rvangelder11/Tube_Clock/code/Parola_Fonts_data.h

// Data file for UTF-8 example user defined fonts
#pragma once

MD_MAX72XX::fontType_t ExtASCII[] PROGMEM =
{
  0,		// 0 - 'Unused'
  0,		// 1 - 'Unused'
  0,		// 2 - 'Unused'
  0,		// 3 - 'Unused'
  0,		// 4 - 'Unused'
  0,		// 5 - 'Unused'
  0,		// 6 - 'Unused'
  0,		// 7 - 'Unused'
  0,		// 8 - 'Unused'
  0,		// 9 - 'Unused'
  0,		// 10 - 'Unused'
  0,		// 11 - 'Unused'
  0,		// 12 - 'Unused'
  0,		// 13 - 'Unused'
  0,		// 14 - 'Unused'
  0,		// 15 - 'Unused'
  0,		// 16 - 'Unused'
  0,		// 17 - 'Unused'
  0,		// 18 - 'Unused'
  0,		// 19 - 'Unused'
  0,		// 20 - 'Unused'
  0,		// 21 - 'Unused'
  0,		// 22 - 'Unused'
  0,		// 23 - 'Unused'
  0,		// 24 - 'Unused'
  0,		// 25 - 'Unused'
  0,		// 26 - 'Unused'
  0,		// 27 - 'Unused'
  0,		// 28 - 'Unused'
  0,		// 29 - 'Unused'
  0,		// 30 - 'Unused'
  0,		// 31 - 'Unused'
  2, 0, 0,		// 32 - 'Space'
  1, 95,		// 33 - '!'
  3, 7, 0, 7,		// 34 - '"'
  5, 20, 127, 20, 127, 20,		// 35 - '#'
  5, 36, 42, 127, 42, 18,		// 36 - '$'
  5, 35, 19, 8, 100, 98,		// 37 - '%'
  5, 54, 73, 86, 32, 80,		// 38 - '&'
  2, 4, 3,		// 39
  3, 28, 34, 65,		// 40 - '('
  3, 65, 34, 28,		// 41 - ')'
  5, 42, 28, 127, 28, 42,		// 42 - '*'
  5, 8, 8, 62, 8, 8,		// 43 - '+'
  2, 128, 96,		// 44 - ','
  5, 8, 8, 8, 8, 8,		// 45 - '-'
  2, 96, 96,		// 46 - '.'
  5, 32, 16, 8, 4, 2,		// 47 - '/'
  5, 62, 81, 73, 69, 62,		// 48 - '0'
  3, 66, 127, 64,		// 49 - '1'
  5, 114, 73, 73, 73, 70,		// 50 - '2'
  5, 33, 65, 73, 77, 51,		// 51 - '3'
  5, 24, 20, 18, 127, 16,		// 52 - '4'
  5, 39, 69, 69, 69, 57,		// 53 - '5'
  5, 60, 74, 73, 73, 49,		// 54 - '6'
  5, 65, 33, 17, 9, 7,		// 55 - '7'
  5, 54, 73, 73, 73, 54,		// 56 - '8'
  5, 70, 73, 73, 41, 30,		// 57 - '9'
  1, 20,		// 58 - ':'
  2, 128, 104,		// 59 - ';'
  4, 8, 20, 34, 65,		// 60 - '<'
  5, 20, 20, 20, 20, 20,		// 61 - '='
  4, 65, 34, 20, 8,		// 62 - '>'
  5, 2, 1, 89, 9, 6,		// 63 - '?'
  5, 62, 65, 93, 89, 78,		// 64 - '@'
  5, 124, 18, 17, 18, 124,		// 65 - 'A'
  5, 127, 73, 73, 73, 54,		// 66 - 'B'
  5, 62, 65, 65, 65, 34,		// 67 - 'C'
  5, 127, 65, 65, 65, 62,		// 68 - 'D'
  5, 127, 73, 73, 73, 65,		// 69 - 'E'
  5, 127, 9, 9, 9, 1,		// 70 - 'F'
  5, 62, 65, 65, 81, 115,		// 71 - 'G'
  5, 127, 8, 8, 8, 127,		// 72 - 'H'
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
  0,		// 127 - 'Unused'
  6, 20, 62, 85, 85, 65, 34,		// 128 - 'Euro sign'
  0,		// 129 - 'Not used'
  2, 128, 96,		// 130 - 'Single low 9 quotation mark'
  5, 192, 136, 126, 9, 3,		// 131 - 'f with hook'
  4, 128, 96, 128, 96,		// 132 - 'Single low 9 quotation mark'
  8, 96, 96, 0, 96, 96, 0, 96, 96,		// 133 - 'Horizontal ellipsis'
  3, 4, 126, 4,		// 134 - 'Dagger'
  3, 20, 126, 20,		// 135 - 'Double dagger'
  4, 2, 1, 1, 2,		// 136 - 'Modifier circumflex'
  7, 35, 19, 104, 100, 2, 97, 96,		// 137 - 'Per mille sign'
  5, 72, 85, 86, 85, 36,		// 138 - 'S with caron'
  3, 8, 20, 34,		// 139 - '< quotation'
  6, 62, 65, 65, 127, 73, 73,		// 140 - 'OE'
  0,		// 141 - 'Not used'
  5, 68, 101, 86, 77, 68,		// 142 - 'z with caron'
  0,		// 143 - 'Not used'
  0,		// 144 - 'Not used'
  2, 3, 4,		// 145 - 'Left single quote mark'
  2, 4, 3,		// 146 - 'Right single quote mark'
  4, 3, 4, 3, 4,		// 147 - 'Left double quote marks'
  4, 4, 3, 4, 3,		// 148 - 'Right double quote marks'
  4, 0, 24, 60, 24,		// 149 - 'Bullet Point'
  3, 8, 8, 8,		// 150 - 'En dash'
  5, 8, 8, 8, 8, 8,		// 151 - 'Em dash'
  4, 2, 1, 2, 1,		// 152 - 'Small ~'
  7, 1, 15, 1, 0, 15, 2, 15,		// 153 - 'TM'
  5, 72, 85, 86, 85, 36,		// 154 - 's with caron'
  3, 34, 20, 8,		// 155 - '> quotation'
  7, 56, 68, 68, 124, 84, 84, 8,		// 156 - 'oe'
  0,		// 157 - 'Not used'
  5, 68, 101, 86, 77, 68,		// 158 - 'z with caron'
  5, 12, 17, 96, 17, 12,		// 159 - 'Y diaresis'
  2, 0, 0,		// 160 - 'Non-breaking space'
  1, 125,		// 161 - 'Inverted !'
  5, 60, 36, 126, 36, 36,		// 162 - 'Cent sign'
  5, 72, 126, 73, 65, 102,		// 163 - 'Pound sign'
  5, 34, 28, 20, 28, 34,		// 164 - 'Currency sign'
  5, 43, 47, 252, 47, 43,		// 165 - 'Yen'
  1, 119,		// 166 - '|'
  4, 102, 137, 149, 106,		// 167 - 'Section sign'
  3, 1, 0, 1,		// 168 - 'Spacing diaresis'
  7, 62, 65, 93, 85, 85, 65, 62,		// 169 - 'Copyright'
  3, 13, 13, 15,		// 170 - 'Feminine Ordinal Ind.'
  5, 8, 20, 42, 20, 34,		// 171 - '<<'
  5, 8, 8, 8, 8, 56,		// 172 - 'Not sign'
  0,		// 173 - 'Soft Hyphen'
  7, 62, 65, 127, 75, 117, 65, 62,		// 174 - 'Registered Trademark'
  5, 1, 1, 1, 1, 1,		// 175 - 'Spacing Macron Overline'
  3, 2, 5, 2,		// 176 - 'Degree'
  5, 68, 68, 95, 68, 68,		// 177 - '+/-'
  3, 25, 21, 19,		// 178 - 'Superscript 2'
  3, 17, 21, 31,		// 179 - 'Superscript 3'
  2, 2, 1,		// 180 - 'Acute accent'
  4, 252, 64, 64, 60,		// 181 - 'micro (mu)'
  5, 6, 9, 127, 1, 127,		// 182 - 'Paragraph Mark'
  2, 24, 24,		// 183 - 'Middle Dot'
  3, 128, 128, 96,		// 184 - 'Spacing sedilla'
  2, 2, 31,		// 185 - 'Superscript 1'
  4, 6, 9, 9, 6,		// 186 - 'Masculine Ordinal Ind.'
  5, 34, 20, 42, 20, 8,		// 187 - '>>'
  6, 64, 47, 16, 40, 52, 250,		// 188 - '1/4'
  6, 64, 47, 16, 200, 172, 186,		// 189 - '1/2'
  6, 85, 53, 31, 40, 52, 250,		// 190 - '3/4'
  5, 48, 72, 77, 64, 32,		// 191 - 'Inverted ?'
  5, 120, 20, 21, 22, 120,		// 192 - 'A grave'
  5, 120, 22, 21, 20, 120,		// 193 - 'A acute'
  5, 122, 21, 21, 21, 122,		// 194 - 'A circumflex'
  5, 120, 22, 21, 22, 121,		// 195 - 'A tilde'
  5, 120, 21, 20, 21, 120,		// 196 - 'A diaresis'
  5, 120, 20, 21, 20, 120,		// 197 - 'A ring above'
  6, 124, 10, 9, 127, 73, 73,		// 198 - 'AE'
  5, 30, 161, 161, 97, 18,		// 199 - 'C sedilla'
  4, 124, 85, 86, 68,		// 200 - 'E grave'
  4, 124, 86, 85, 68,		// 201 - 'E acute'
  4, 126, 85, 85, 70,		// 202 - 'E circumflex'
  4, 124, 85, 84, 69,		// 203 - 'E diaresis'
  3, 68, 125, 70,		// 204 - 'I grave'
  3, 68, 126, 69,		// 205 - 'I acute'
  3, 70, 125, 70,		// 206 - 'I circumplex'
  3, 69, 124, 69,		// 207 - 'I diaresis'
  6, 4, 127, 69, 65, 65, 62,		// 208 - 'Capital Eth'
  5, 124, 10, 17, 34, 125,		// 209 - 'N tilde'
  5, 56, 68, 69, 70, 56,		// 210 - 'O grave'
  5, 56, 70, 69, 68, 56,		// 211 - 'O acute'
  5, 58, 69, 69, 69, 58,		// 212 - 'O circumflex'
  5, 56, 70, 69, 70, 57,		// 213 - 'O tilde'
  5, 56, 69, 68, 69, 56,		// 214 - 'O diaresis'
  5, 34, 20, 8, 20, 34,		// 215 - 'Multiplication sign'
  7, 64, 62, 81, 73, 69, 62, 1,		// 216 - 'O slashed'
  5, 60, 65, 66, 64, 60,		// 217 - 'U grave'
  5, 60, 64, 66, 65, 60,		// 218 - 'U acute'
  5, 58, 65, 65, 65, 58,		// 219 - 'U circumflex'
  5, 60, 65, 64, 65, 60,		// 220 - 'U diaresis'
  5, 12, 16, 98, 17, 12,		// 221 - 'Y acute'
  4, 127, 18, 18, 12,		// 222 - 'Capital thorn'
  4, 254, 37, 37, 26,		// 223 - 'Small letter sharp S'
  5, 32, 84, 85, 122, 64,		// 224 - 'a grave'
  5, 32, 84, 86, 121, 64,		// 225 - 'a acute'
  5, 34, 85, 85, 121, 66,		// 226 - 'a circumflex'
  5, 32, 86, 85, 122, 65,		// 227 - 'a tilde'
  5, 32, 85, 84, 121, 64,		// 228 - 'a diaresis'
  5, 32, 84, 85, 120, 64,		// 229 - 'a ring above'
  7, 32, 84, 84, 124, 84, 84, 8,		// 230 - 'ae'
  5, 24, 36, 164, 228, 40,		// 231 - 'c sedilla'
  5, 56, 84, 85, 86, 88,		// 232 - 'e grave'
  5, 56, 84, 86, 85, 88,		// 233 - 'e acute'
  5, 58, 85, 85, 85, 90,		// 234 - 'e circumflex'
  5, 56, 85, 84, 85, 88,		// 235 - 'e diaresis'
  3, 68, 125, 66,		// 236 - 'i grave'
  3, 68, 126, 65,		// 237 - 'i acute'
  3, 70, 125, 66,		// 238 - 'i circumflex'
  3, 69, 124, 65,		// 239 - 'i diaresis'
  4, 48, 75, 74, 61,		// 240 - 'Small eth'
  4, 122, 9, 10, 113,		// 241 - 'n tilde'
  5, 56, 68, 69, 70, 56,		// 242 - 'o grave'
  5, 56, 70, 69, 68, 56,		// 243 - 'o acute'
  5, 58, 69, 69, 69, 58,		// 244 - 'o circumflex'
  5, 56, 70, 69, 70, 57,		// 245 - 'o tilde'
  5, 56, 69, 68, 69, 56,		// 246 - 'o diaresis'
  5, 8, 8, 42, 8, 8,		// 247 - 'Division sign'
  6, 64, 56, 84, 76, 68, 58,		// 248 - 'o slashed'
  5, 60, 65, 66, 32, 124,		// 249 - 'u grave'
  5, 60, 64, 66, 33, 124,		// 250 - 'u acute'
  5, 58, 65, 65, 33, 122,		// 251 - 'u circumflex'
  5, 60, 65, 64, 33, 124,		// 252 - 'u diaresis'
  4, 156, 162, 161, 124,		// 253 - 'y acute'
  4, 252, 72, 72, 48,		// 254 - 'small thorn'
  4, 157, 160, 160, 125,		// 255 - 'y diaresis'
};
