rvangelder11/Tube_Clock/code/utf8AsciiChar.ino

void utf8AsciiString(char* s)
// In place conversion UTF-8 string to Extended ASCII
// The extended ASCII string is always shorter.
{
  uint8_t c;
  char *cp = s;


  while (*s != '\0')
  {
    c = utf8AsciiChar(*s++);
    if (c != '\0')
      *cp++ = c;
  }
  *cp = '\0';   // terminate the new string
}
